klubieniecki/brium-board/brand/brium-board-outline-3px.png

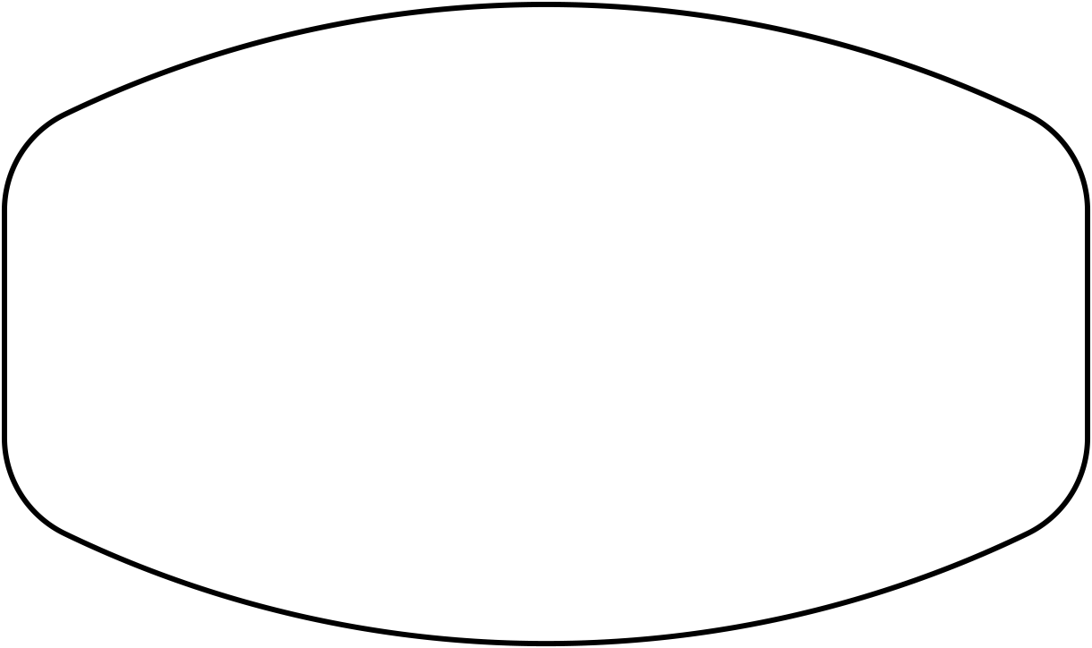
brand/brium-board-outline-3px.png
