klubieniecki/brium-board/brand/brium-mark-512.png

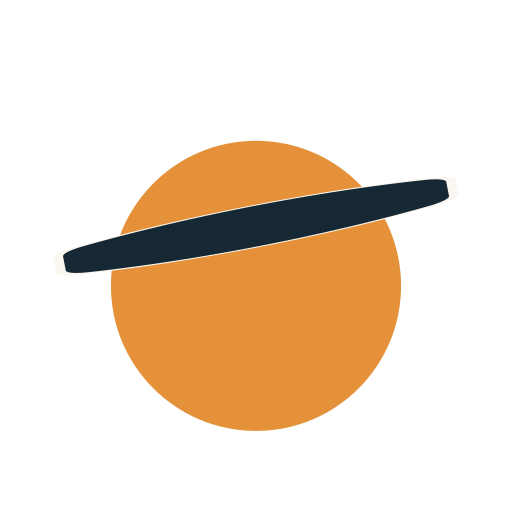
brand/brium-mark-512.png
